ChadPauley/HapticFeedbackSystem/Additional_Files/1.PNG

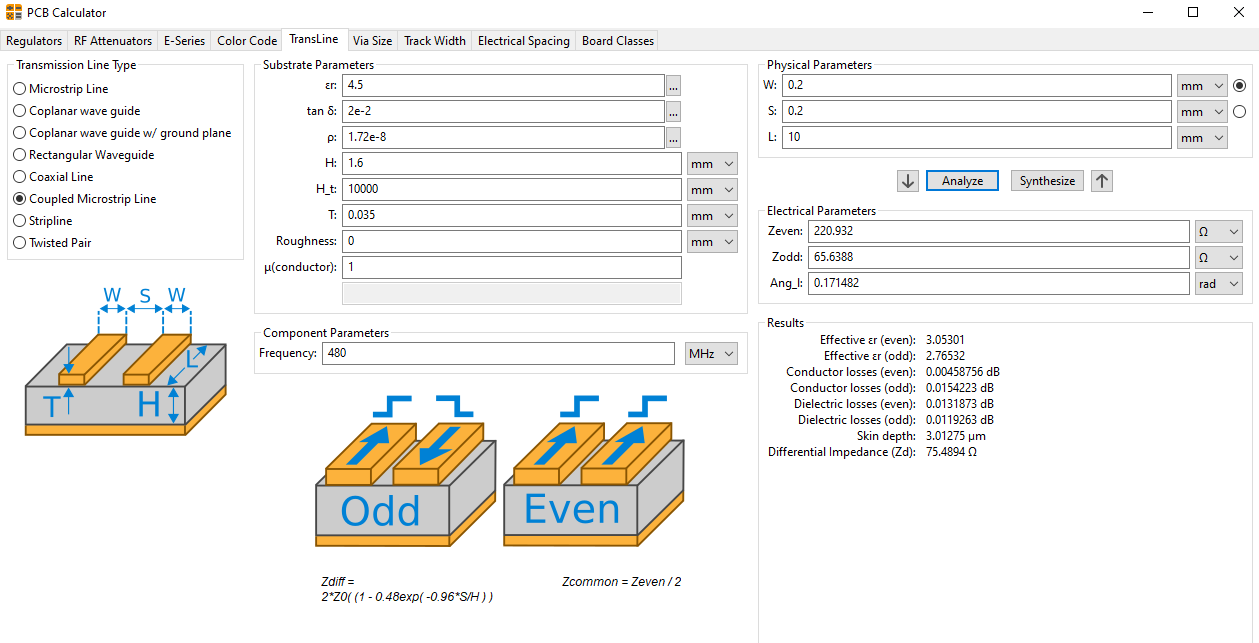
Additional_Files/1.PNG
