ChadPauley/HapticFeedbackSystem/Additional_Files/2.PNG

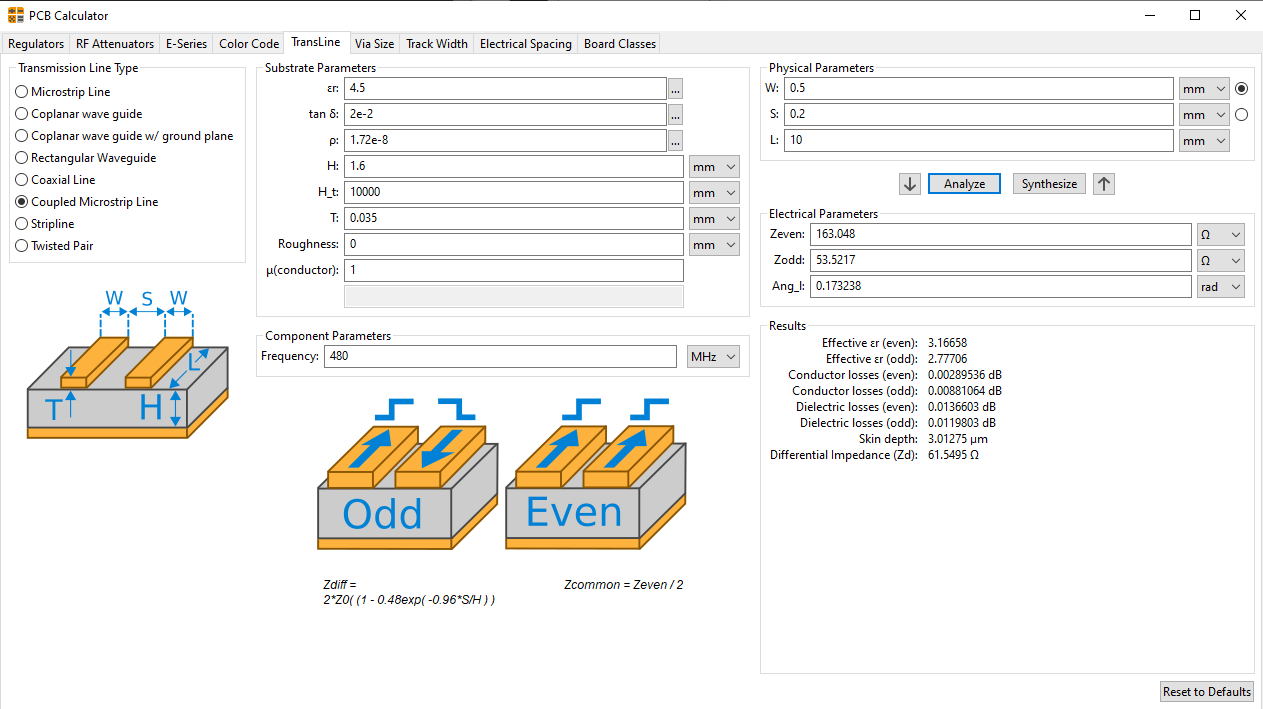
Additional_Files/2.PNG
