ChadPauley/HapticFeedbackSystem/Additional_Files/4 GPIO Module.PNG

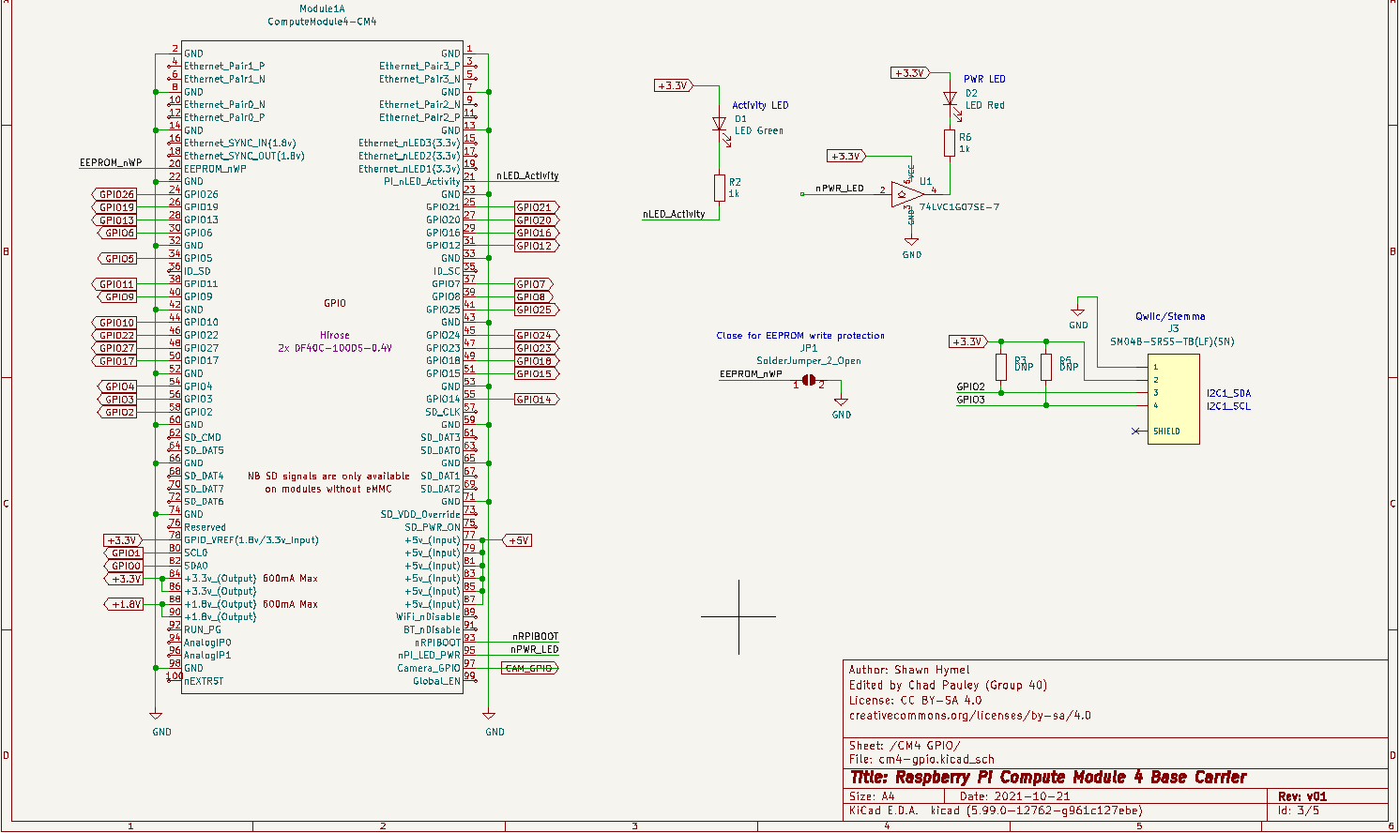
Additional_Files/4 GPIO Module.PNG
