ChadPauley/HapticFeedbackSystem/Additional_Files/5 power.PNG

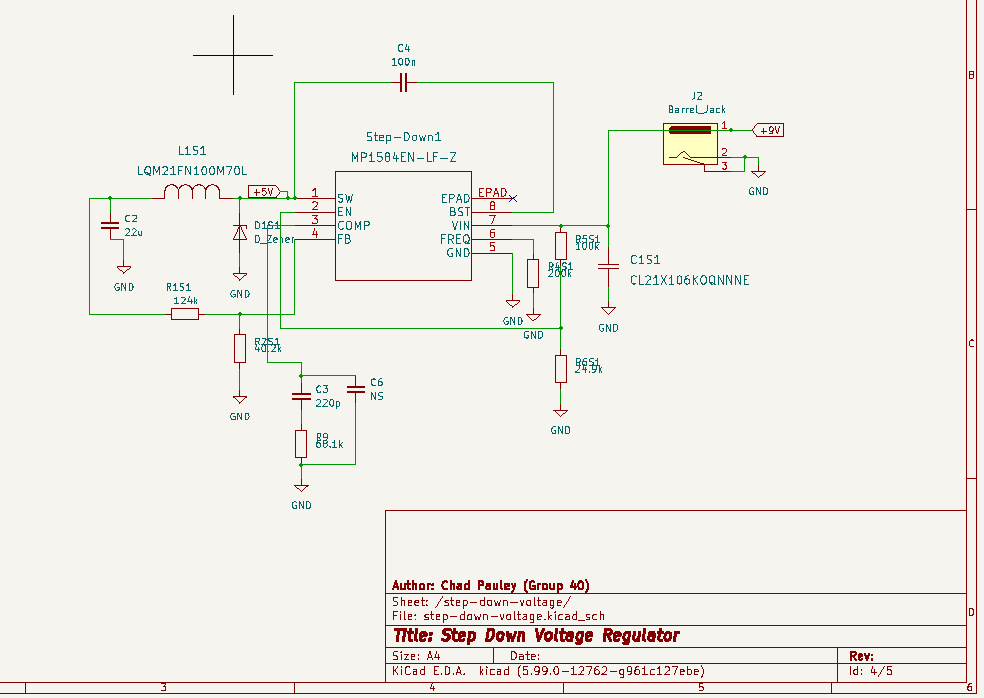
Additional_Files/5 power.PNG
