ChadPauley/HapticFeedbackSystem/Additional_Files/6 Serial Communication.PNG

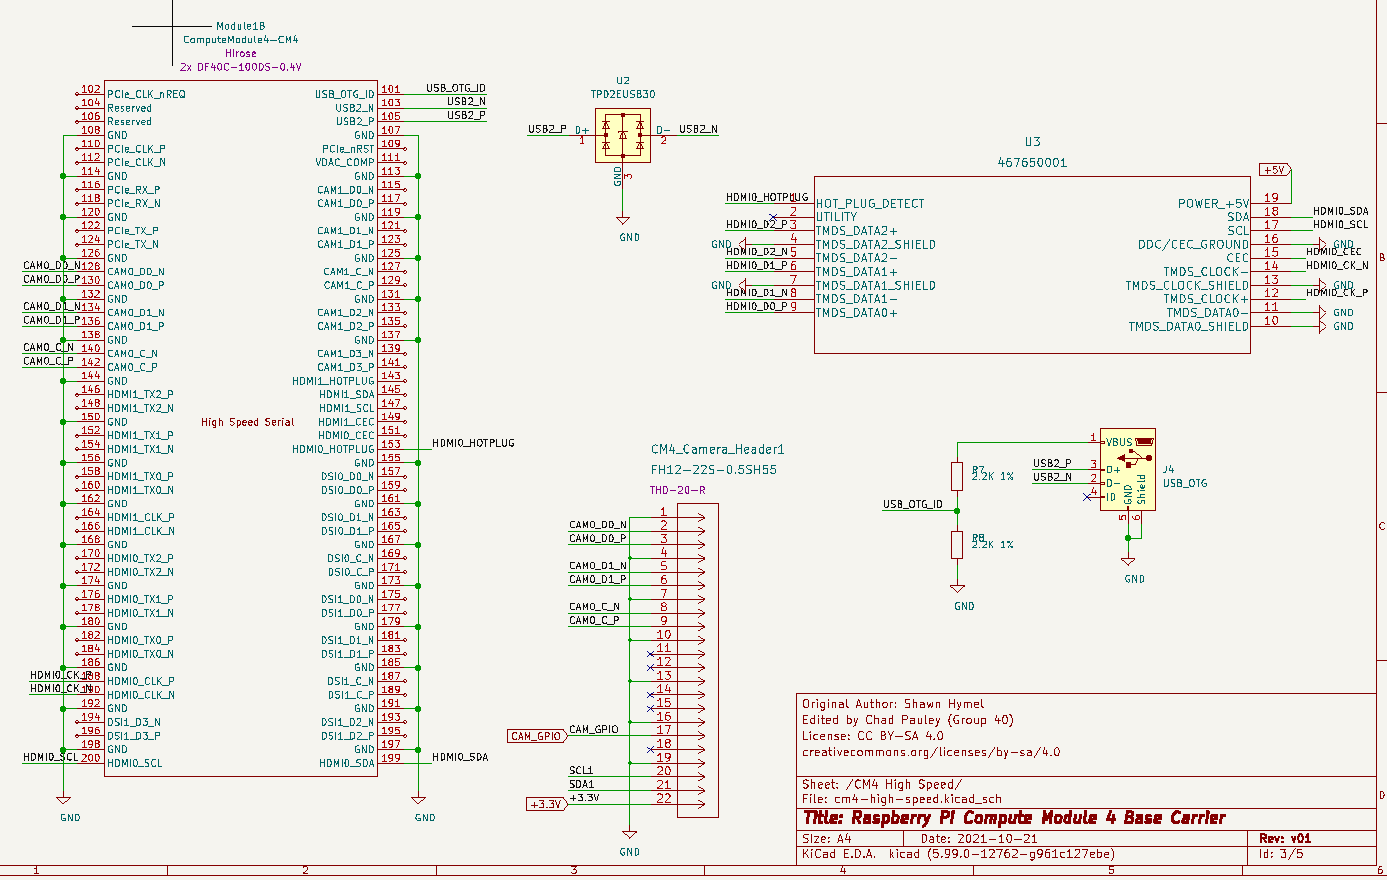
Additional_Files/6 Serial Communication.PNG
