ChadPauley/HapticFeedbackSystem/Additional_Files/7 button and motor pin header.PNG

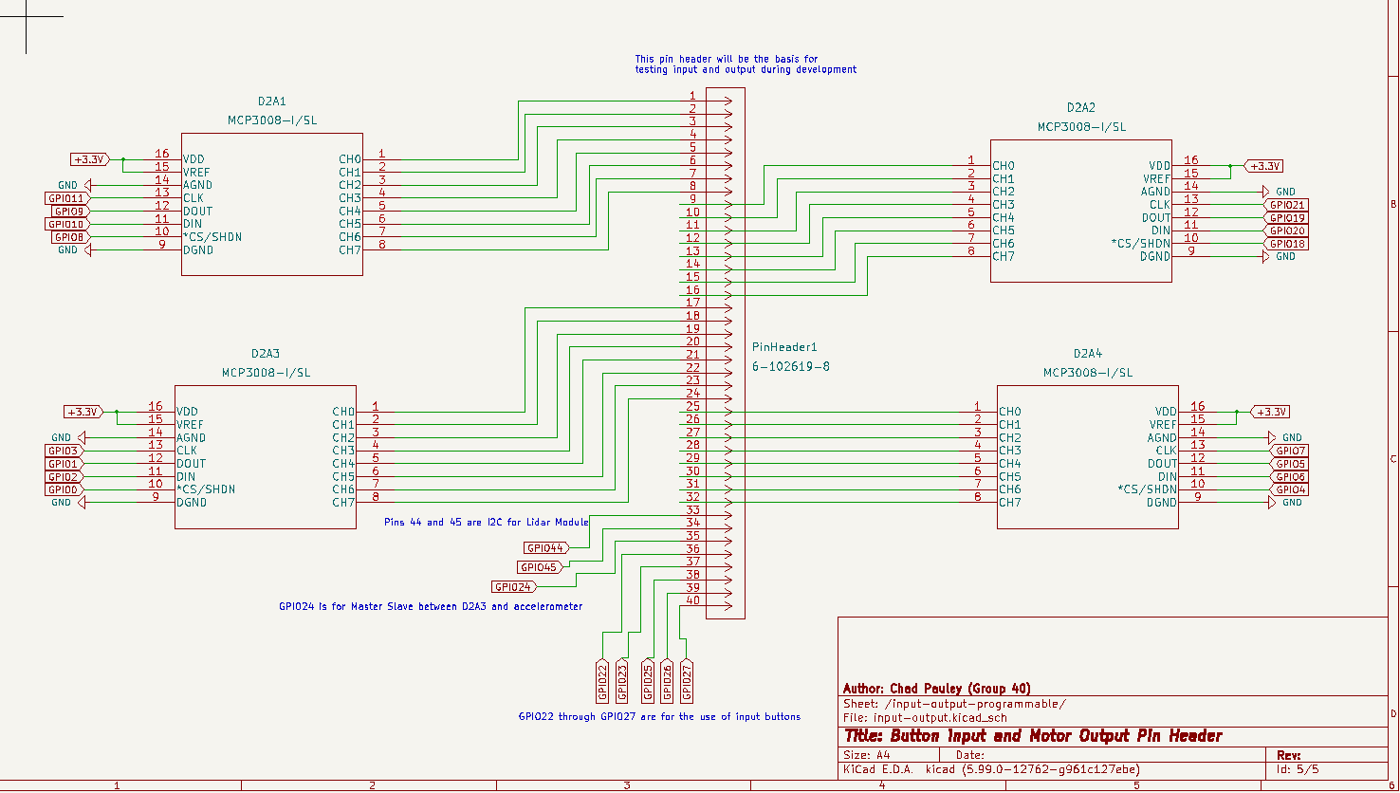
Additional_Files/7 button and motor pin header.PNG
