ChadPauley/HapticFeedbackSystem/Additional_Files/board 3d.PNG

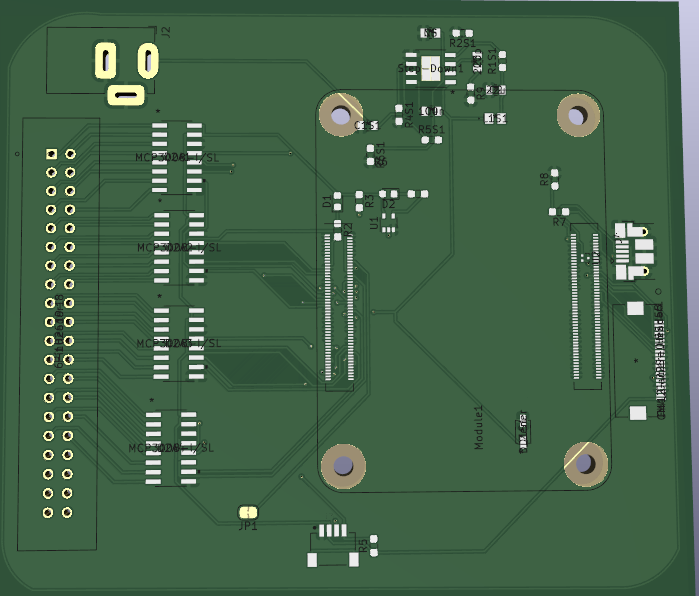
Additional_Files/board 3d.PNG
