ChadPauley/HapticFeedbackSystem/Additional_Files/Ratsnest.PNG

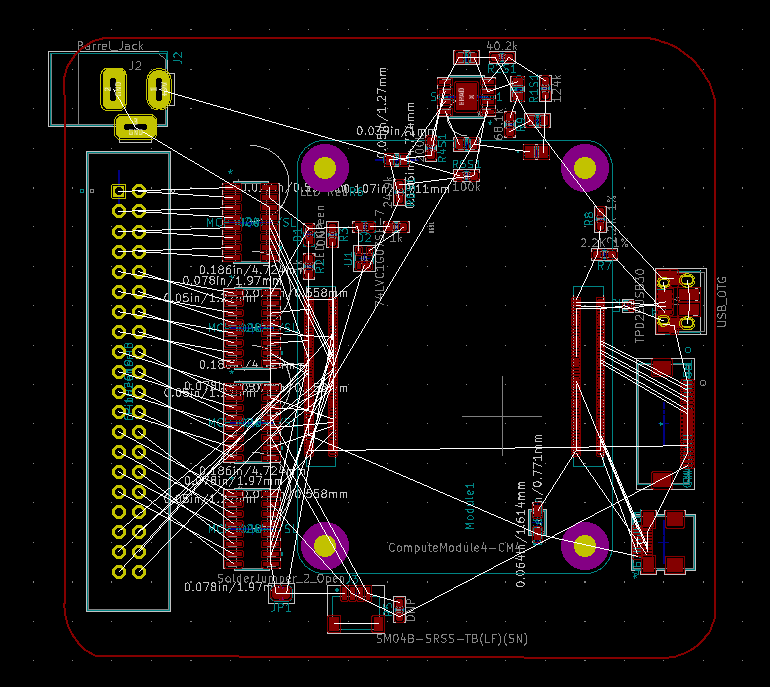
Additional_Files/Ratsnest.PNG
